ryomuk/XYamp/hardware/rev0.1/XYamp.kicad_sch

## KiCad design hardware/rev0.1/XYamp.kicad_sch (2023-10-17)

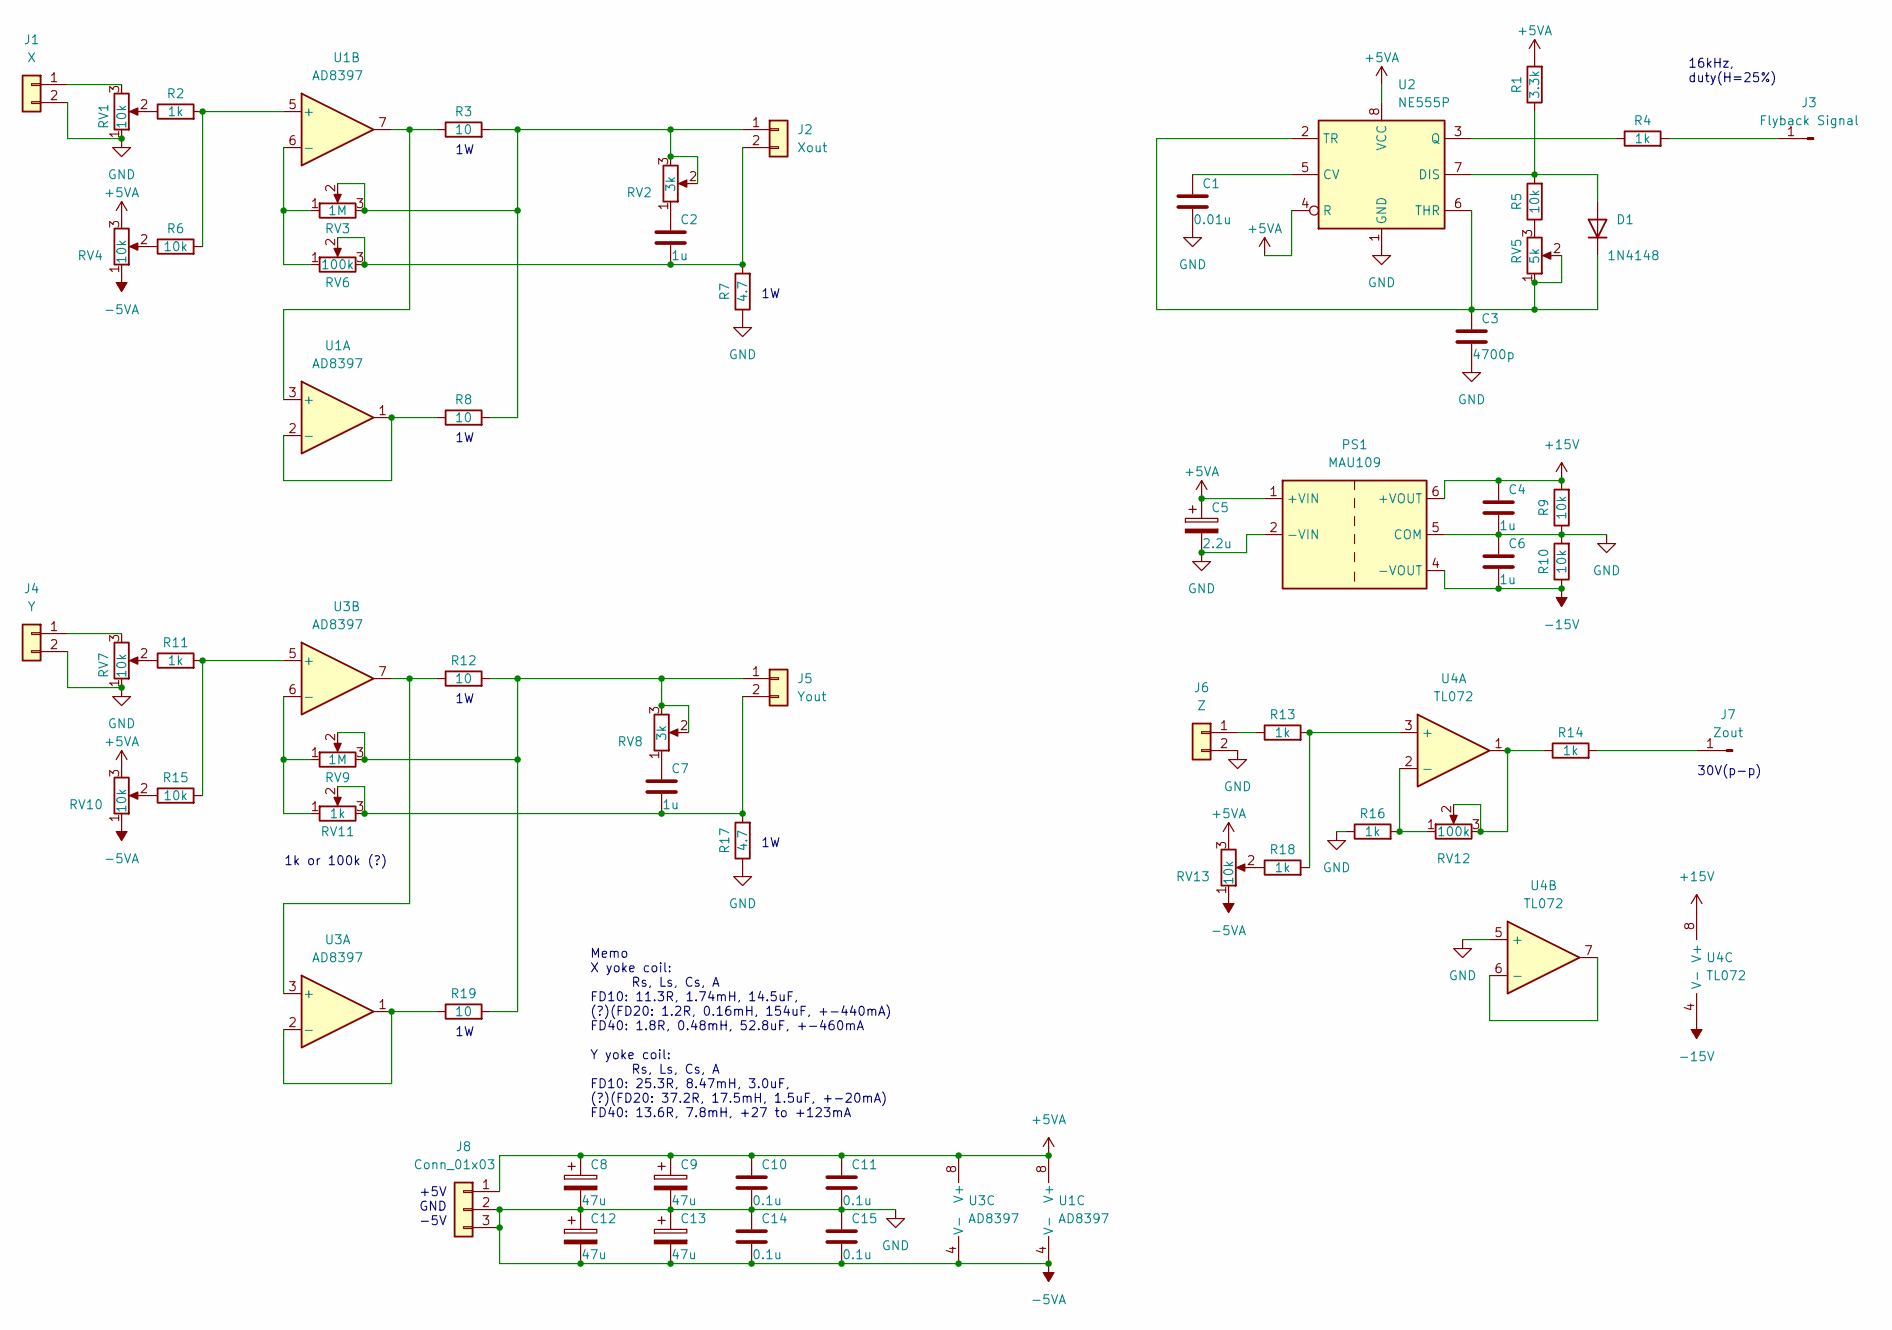
[picture p20: schematic XYamp.kicad_sch]

Parts:
C1: 0.01u
C2, C4, C6, C7: 1u
C3: 4700p
C5: 2.2u
C8, C9, C12, C13: 47u
C10, C11, C14, C15: 0.1u
D1: 1N4148
J1: X
J2: Xout
J3: Flyback Signal
J4: Y
J5: Yout
J6: Z
J7: Zout
J8: Conn_01x03
PS1: MAU109; SIP-6_without_3pin_for_DCDC_MAU
R1: 3.3k
R2, R4, R11, R13, R14, R16, R18: 1k
R3, R8, R12, R19: 10
R5, R6, R9, R10, R15: 10k
R7, R17: 4.7
RV1, RV4, RV7, RV10, RV13: 10k
RV2, RV8: 3k
RV3, RV9: 1M
RV5: 5k
RV6, RV12: 100k
RV11: 1k
U1, U3: AD8397; SOIC-8-1EP_3.9x4.9mm_P1.27mm_EP2.29x3mm_ThermalVias
U2: NE555P; DIP-8_W7.62mm
U4: TL072

Connections:
+5VA: C5.1, C8.1, C9.1, C10.1, C11.1, J8.1, PS1.1 (+VIN), R1.2, RV4.3, RV10.3, RV13.3, U1.8 (V+), U2.4 (R), U2.8 (VCC), U3.8 (V+)
+15V: C4.1, PS1.6 (+VOUT), R9.2, U4.8 (V+)
-5VA: C1.2, C3.2, C4.2, C5.2, C6.1, C8.2, C9.2, C10.2, C11.2, C12.1, C12.2, C13.1, C13.2, C14.1, C14.2, C15.1, C15.2, J1.2, J4.2, J6.2, J8.2, J8.3, PS1.2 (-VIN), PS1.5 (COM), R7.1, R9.1, R10.2, R16.1, R17.1, RV1.1, RV4.1, RV7.1, RV10.1, RV13.1, U1.4 (V-), U2.1 (GND), U3.4 (V-), U4.5 (+)
-15V: C6.2, PS1.4 (-VOUT), R10.1, U4.4 (V-)
unnamed: C1.1, U2.5 (CV)
unnamed: C2.1, RV2.1
unnamed: C2.2, J2.2, R7.2, RV6.2, RV6.3
unnamed: C3.1, D1.1 (K), RV5.1, RV5.2, U2.2 (TR), U2.6 (THR)
unnamed: C7.1, RV8.1
unnamed: C7.2, J5.2, R17.2, RV11.2, RV11.3
unnamed: D1.2 (A), R1.1, R5.2, U2.7 (DIS)
unnamed: J1.1, RV1.3
unnamed: J2.1, R3.2, R8.2, RV2.2, RV2.3, RV3.2, RV3.3
unnamed: J3.1, R4.2
unnamed: J4.1, RV7.3
unnamed: J5.1, R12.2, R19.2, RV8.2, RV8.3, RV9.2, RV9.3
unnamed: J6.1, R13.1
unnamed: J7.1, R14.2
unnamed: R2.1, RV1.2
unnamed: R2.2, R6.2, U1.5 (+)
unnamed: R3.1, U1.3 (+), U1.7
unnamed: R4.1, U2.3 (Q)
unnamed: R5.1, RV5.3
unnamed: R6.1, RV4.2
unnamed: R8.1, U1.1, U1.2 (-)
unnamed: R11.1, RV7.2
unnamed: R11.2, R15.2, U3.5 (+)
unnamed: R12.1, U3.3 (+), U3.7
unnamed: R13.2, R18.2, U4.3 (+)
unnamed: R14.1, RV12.2, RV12.3, U4.1
unnamed: R15.1, RV10.2
unnamed: R16.2, RV12.1, U4.2 (-)
unnamed: R18.1, RV13.2
unnamed: R19.1, U3.1, U3.2 (-)
unnamed: RV3.1, RV6.1, U1.6 (-)
unnamed: RV9.1, RV11.1, U3.6 (-)
unnamed: U4.6 (-), U4.7

Notes on the sheet:
16kHz, duty(H=25%)
Memo X yoke coil: Rs, Ls, Cs, A FD10: 11.3R, 1.74mH, 14.5uF, (?)(FD20: 1.2R, 0.16mH, 154uF, +-440mA) FD40: 1.8R, 0.48mH, 52.8uF, +-460mA Y yoke coil: Rs, Ls, Cs, A FD10: 25.3R, 8.47mH, 3.0uF, (?)(FD20: 37.2R, 17.5mH, 1.5uF, +-20mA) FD40: 13.6R, 7.8mH, +27 to +123mA
30V(p-p)
1k or 100k (?)
+5V GND -5V
